andiling/Wireless-DS18B20-ESP8266/img/AN148-ImprovedCPUBusInterface.jpg

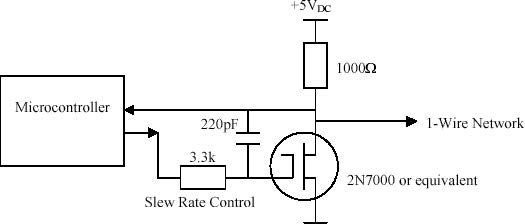
img/AN148-ImprovedCPUBusInterface.jpg
