andiling/Wireless-DS18B20-ESP8266/img/config.png

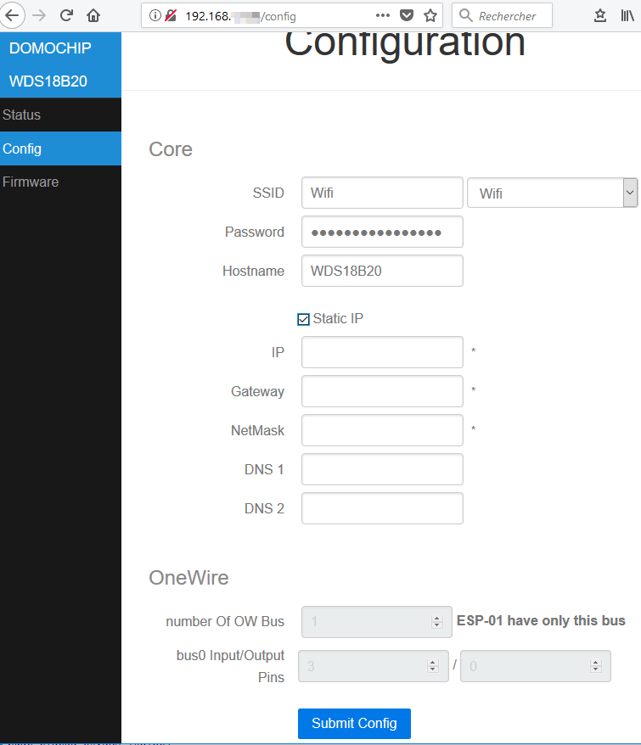
img/config.png
