andiling/Wireless-DS18B20-ESP8266/img/JeedomScriptAdd.png

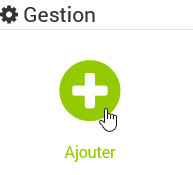
img/JeedomScriptAdd.png
