andiling/Wireless-DS18B20-ESP8266/img/JeedomScriptAddCmd.png

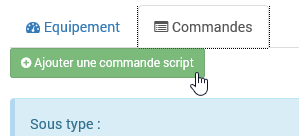
img/JeedomScriptAddCmd.png
