andiling/Wireless-DS18B20-ESP8266/img/JeedomScriptRefresh.png

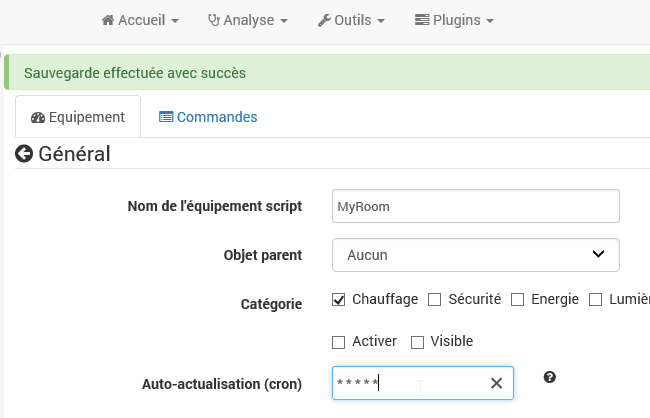
img/JeedomScriptRefresh.png
