andiling/Wireless-DS18B20-ESP8266/img/status.png

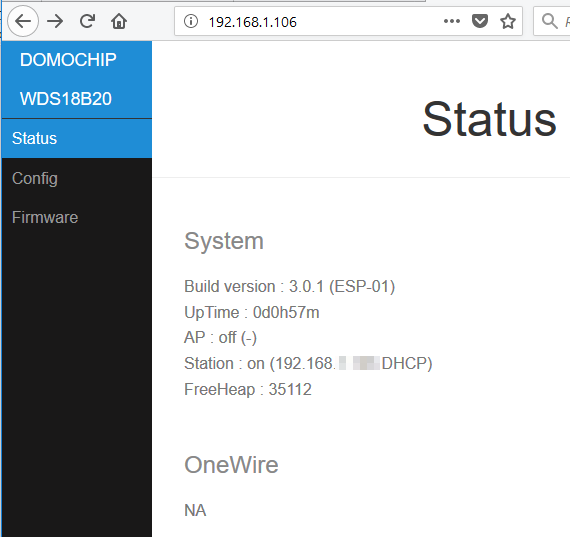
img/status.png
