andiling/Wireless-DS18B20-ESP8266/img/JeedomScriptResult.png

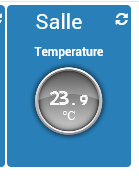
img/JeedomScriptResult.png
